fitch/SVI-3x8-PicoExpander/pico/c/launcher_bk4x.h

static const uint8_t LAUNCHER_BK4X[] = {
  0xcf, 0x00, 0x00, 0xc3, 0x5d, 0x00, 0x00, 0x00, 0xc3, 0x10, 0xfb, 0x00,
  0x00, 0x00, 0x00, 0x00, 0xc3, 0xe9, 0x60, 0x00, 0x00, 0x00, 0x00, 0x00,
  0x00, 0x00, 0x00, 0x00, 0x00, 0x00, 0x00, 0x00, 0xc3, 0x23, 0x00, 0xc9,
  0xc9, 0xc9, 0xc9, 0xc9, 0x00, 0x00, 0x00, 0x00, 0x00, 0x00, 0x00, 0x00,
  0xc3, 0xf1, 0x60, 0xc3, 0xcc, 0x68, 0x01, 0x00, 0xf5, 0x08, 0xf5, 0xc5,
  0xd5, 0xe5, 0xdd, 0xe5, 0xfd, 0xe5, 0xcd, 0x57, 0x00, 0x21, 0x89, 0x09,
  0x34, 0xfd, 0xe1, 0xdd, 0xe1, 0xe1, 0xd1, 0xc1, 0xf1, 0x08, 0xcd, 0x42,
  0xfb, 0xf1, 0xfb, 0xc9, 0xe9, 0xdd, 0xe9, 0xfd, 0xe9, 0xf3, 0x21, 0x00,
  0xf1, 0x11, 0x00, 0x71, 0x01, 0x00, 0x0f, 0xed, 0xb0, 0xf3, 0x3e, 0x0f,
  0xd3, 0x88, 0xdb, 0x90, 0xe6, 0x20, 0xf6, 0xc1, 0xd3, 0x8c, 0xed, 0x73,
  0x20, 0xf0, 0x31, 0x00, 0xf1, 0x21, 0x00, 0x71, 0x11, 0x00, 0xf1, 0x01,
  0x00, 0x0f, 0xed, 0xb0, 0x21, 0xde, 0x6e, 0x11, 0x10, 0xfb, 0x01, 0x2d,
  0x01, 0xed, 0xb0, 0xcd, 0x73, 0x19, 0xc4, 0xdf, 0x19, 0xaf, 0x32, 0x02,
  0xfa, 0x32, 0x06, 0xfa, 0x32, 0x43, 0x0f, 0x3e, 0x01, 0x32, 0x36, 0x00,
  0x3e, 0x30, 0xd3, 0x13, 0x11, 0x0a, 0xf1, 0x21, 0x1e, 0xfa, 0xaf, 0x72,
  0x14, 0x23, 0x06, 0x0f, 0x77, 0x23, 0x10, 0xfc, 0x1d, 0xc2, 0xb3, 0x00,
  0xcd, 0x50, 0x19, 0xcd, 0xac, 0x18, 0x3a, 0xfe, 0x19, 0xa7, 0xca, 0xfd,
  0x01, 0x3e, 0x04, 0x32, 0xf0, 0x3c, 0x21, 0x10, 0x22, 0xcd, 0xd2, 0x3c,
  0xcd, 0x2d, 0x19, 0x21, 0x8b, 0xfd, 0x22, 0x1a, 0xfa, 0x22, 0x1c, 0xfa,
  0xaf, 0xf3, 0xd3, 0x81, 0x3e, 0x60, 0xfb, 0xd3, 0x81, 0x3e, 0x80, 0x01,
  0x13, 0x00, 0xd3, 0x80, 0x00, 0x10, 0xfb, 0x0d, 0xc2, 0xf2, 0x00, 0x3e,
  0xd0, 0x01, 0x05, 0x00, 0xd3, 0x80, 0x00, 0x10, 0xfb, 0x0d, 0xc2, 0x00,
  0x01, 0x11, 0x1e, 0x1e, 0x0e, 0x01, 0xd5, 0xfb, 0x00, 0x76, 0xf3, 0xc5,
  0xd5, 0x7b, 0xcd, 0xc2, 0x01, 0xd1, 0xd5, 0x7a, 0x2f, 0x3e, 0xf8, 0x83,
  0xba, 0x3f, 0x30, 0x09, 0xfe, 0xc0, 0x30, 0x05, 0x16, 0x00, 0xcd, 0xe3,
  0x01, 0xd1, 0xc1, 0x14, 0x79, 0x3c, 0x4f, 0x7b, 0x81, 0x5f, 0x38, 0x04,
  0xfe, 0xc0, 0x38, 0xd7, 0x3e, 0xbf, 0x16, 0x00, 0xcd, 0xe3, 0x01, 0xd1,
  0x14, 0x1c, 0xcd, 0x91, 0x1f, 0xc2, 0x64, 0x01, 0x7a, 0xfe, 0x5c, 0xcc,
  0x9d, 0x01, 0xfe, 0xbe, 0xc2, 0x0c, 0x01, 0x06, 0xfa, 0xfb, 0xcd, 0x91,
  0x1f, 0xc2, 0x64, 0x01, 0x76, 0xf3, 0x10, 0xf5, 0x06, 0x07, 0x0e, 0x00,
  0xaf, 0xfb, 0x3c, 0xf5, 0x2f, 0x81, 0x4f, 0x76, 0xf3, 0xc5, 0xaf, 0xf3,
  0xd3, 0x81, 0x3e, 0x58, 0xfb, 0xd3, 0x81, 0x06, 0x18, 0x16, 0x00, 0xc5,
  0x06, 0x20, 0x59, 0x1c, 0xfa, 0x8a, 0x01, 0x7b, 0x82, 0x2e, 0xaf, 0xd3,
  0x80, 0x10, 0xf4, 0x7a, 0xc6, 0x20, 0x57, 0xc1, 0x10, 0xe9, 0xc1, 0xf1,
  0x10, 0xcf, 0xc3, 0xf7, 0x01, 0xaf, 0xf3, 0xd3, 0x81, 0x3e, 0x6d, 0xfb,
  0xd3, 0x81, 0x3e, 0xf0, 0x01, 0x0b, 0x00, 0xd3, 0x80, 0x00, 0x10, 0xfb,
  0x0d, 0xc2, 0xab, 0x01, 0xf3, 0xc9, 0x67, 0xe6, 0x07, 0x6f, 0xac, 0x0f,
  0x0f, 0x0f, 0xf6, 0x40, 0x67, 0xc9, 0xcd, 0xb6, 0x01, 0x7a, 0xeb, 0xcd,
  0xb6, 0x01, 0xaa, 0x57, 0x7d, 0xab, 0x5f, 0x01, 0x08, 0x20, 0x7d, 0xab,
  0xd3, 0x81, 0x7c, 0xaa, 0xd3, 0x81, 0x7e, 0xd3, 0x80, 0x7d, 0x81, 0x6f,
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
};
static const uint32_t LAUNCHER_BK4X_len = 48901;

#define DEVICE_ID_ADDRESS 0x000006D9
#define MENU_STATE_ADDRESS 0x00000036
