fitch/SVI-3x8-PicoExpander/pico/c/biospatch.h

static const uint8_t BIOSPATCH[] = {
    0x18, 0x20, 11, 0xcd, 0x84, 0x21, 0x38, 0x2d, 0xc1, 0xd1, 0xc9, 0xc1, 0xd1, 0xc9,
    0x26, 0x20, 6, 0xf5, 0xdb, 0x65, 0xfe, 0xff, 0x28,
    0x2d, 0x20, 4, 0xf1, 0xd3, 0x64, 0xc9,
    0x3e, 0x20, 12, 0xf3, 0xcd, 0x64, 0x21, 0xd2, 0x66, 0x39, 0x00, 0x00, 0x00, 0x00, 0x00,
    0x61, 0x20, 1, 0x89,
    0x6c, 0x20, 12, 0xf5, 0x3e, 0x03, 0xd3, 0x65, 0x3e, 0x09, 0xd3, 0x97, 0xf1, 0xfb, 0xc9,
    0x88, 0x20, 7, 0xc9, 0x3e, 0x02, 0x32, 0x65, 0x00, 0xc9,
    0xd0, 0x20, 2, 0x10, 0x00,
    0xd4, 0x20, 25, 0xcd, 0x26, 0x20, 0x0b, 0x78, 0xb1, 0x20, 0xf6, 0x3e, 0x7f, 0xc3, 0x26, 0x20, 0x00, 0x00, 0x00, 0x00, 0x00, 0x00, 0x00, 0x00, 0x00, 0x00, 0x00, 0x00,
    0x67, 0x21, 2, 0x84, 0x21,
    0x6a, 0x21, 42, 0xfe, 0x55, 0x20, 0xf6, 0x0c, 0xcd, 0x84, 0x21, 0xd8, 0xfe, 0x55, 0x28, 0xf7, 0xfe, 0x7f, 0x20, 0xe9, 0x3e, 0x0a, 0xb9, 0x30, 0xe4, 0xa7, 0xc9, 0xa7, 0xc9, 0xcd, 0x12, 0x35, 0xd8, 0xdb, 0x65, 0xfe, 0xff, 0x28, 0xf6, 0xfe, 0x02, 0x28, 0x08, 0xdb, 0x64,
    0x99, 0x21, 7, 0xc9, 0x3e, 0x01, 0xd3, 0x65, 0x37, 0xc9,
    0x58, 0x7c, 2, 0x97, 0x7f,
    0x97, 0x7f, 25, 0xcd, 0x7d, 0x69, 0x21, 0xa0, 0x7f, 0xc3, 0x7d, 0x69, 0x50, 0x61, 0x74, 0x63, 0x68, 0x65, 0x64, 0x20, 0x66, 0x6f, 0x72, 0x20, 0x74, 0x61, 0x70, 0x65,
    0xb1, 0x7f, 44, 0x65, 0x6d, 0x75, 0x6c, 0x61, 0x74, 0x69, 0x6f, 0x6e, 0x0d, 0x0a, 0x00, 0x00, 0x00, 0x00, 0x00, 0x00, 0x00, 0x00, 0x00, 0x00, 0x00, 0x00, 0x00, 0x00, 0x00, 0x00, 0x00, 0x00, 0x00, 0x00, 0x00, 0x00, 0x00, 0x00, 0x00, 0x00, 0x00, 0x00, 0x00, 0x00, 0x00, 0x00, 0x00,
    0xde, 0x7f, 11, 0x00, 0x00, 0x00, 0x00, 0x00, 0x00, 0x00, 0x00, 0x00, 0x00, 0x00,
    0xea, 0x7f, 21, 0x00, 0x00, 0x00, 0x00, 0x00, 0x00, 0x00, 0x00, 0x00, 0x00, 0x00, 0x00, 0x00, 0x00, 0x00, 0x00, 0x00, 0x00, 0x00, 0x00, 0x00,
    0, 0
};
